Micropickle/vocoder/photos/CAD designs/KiCad/Screenshot from 2026-01-22 20-45-53.png

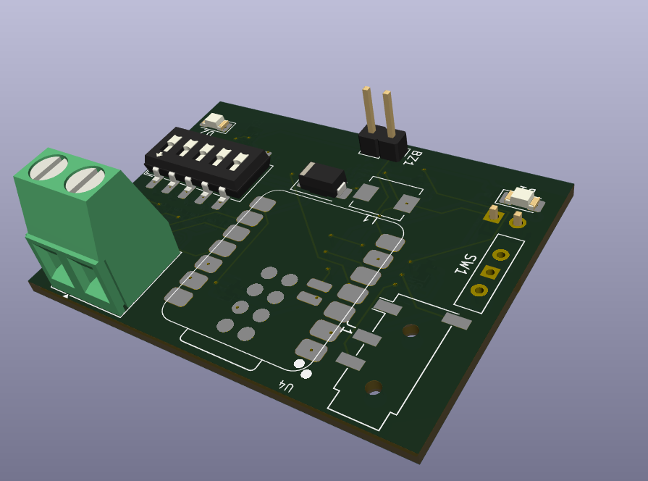
photos/CAD designs/KiCad/Screenshot from 2026-01-22 20-45-53.png
