Micropickle/vocoder/photos/CAD designs/KiCad/Screenshot from 2026-01-23 09-53-42.png

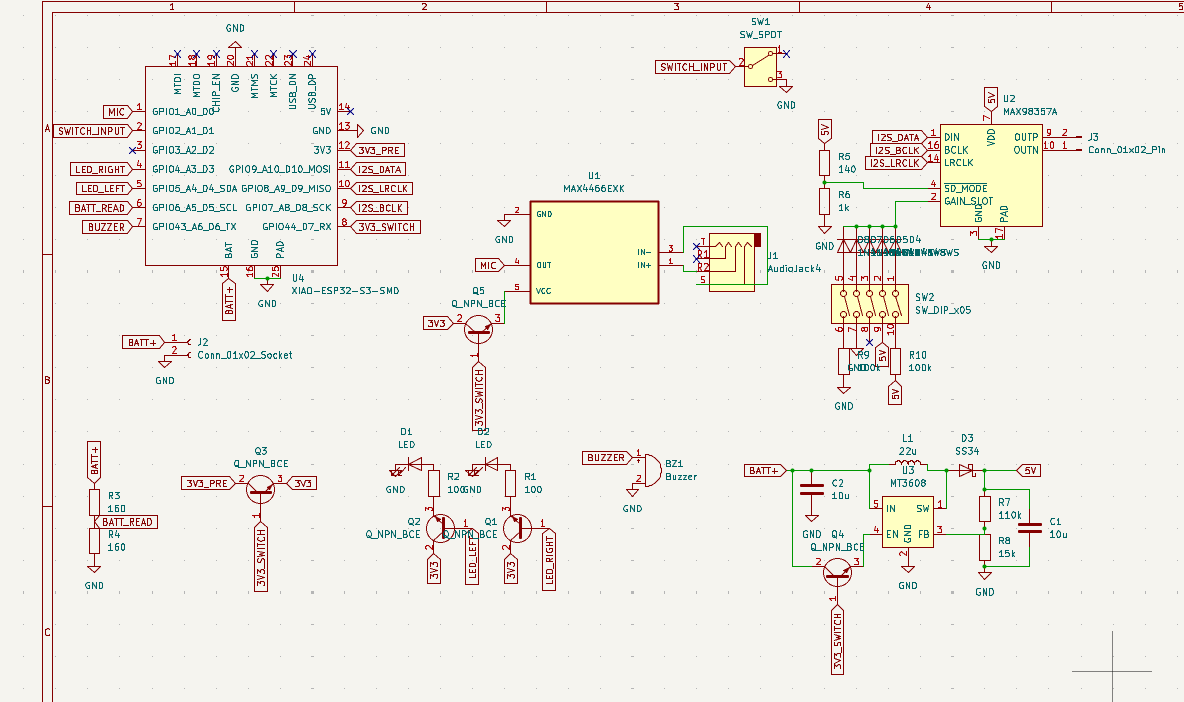
photos/CAD designs/KiCad/Screenshot from 2026-01-23 09-53-42.png
