Micropickle/vocoder/photos/CAD designs/KiCad/Screenshot from 2026-03-05 19-23-13.png

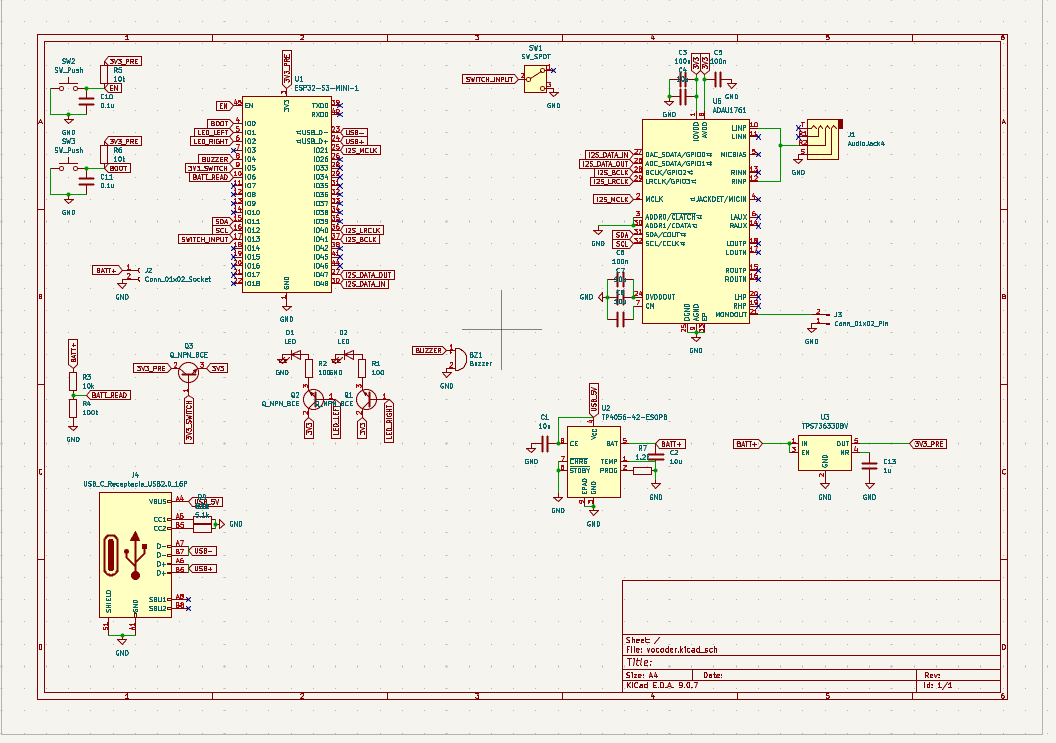
photos/CAD designs/KiCad/Screenshot from 2026-03-05 19-23-13.png
