Micropickle/vocoder/photos/CAD designs/KiCad/Screenshot from 2026-07-01 14-14-26.png

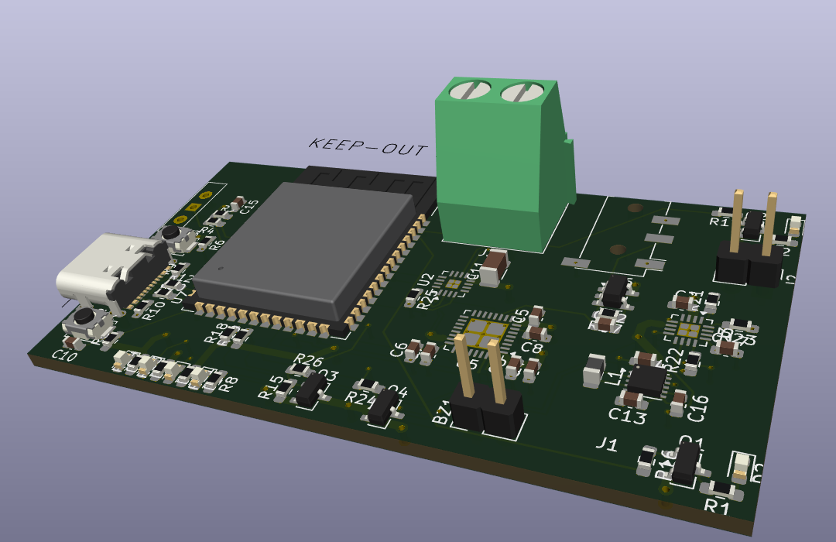
photos/CAD designs/KiCad/Screenshot from 2026-07-01 14-14-26.png
