Micropickle/vocoder/photos/prototype version/IMG_20260123_094632.jpg

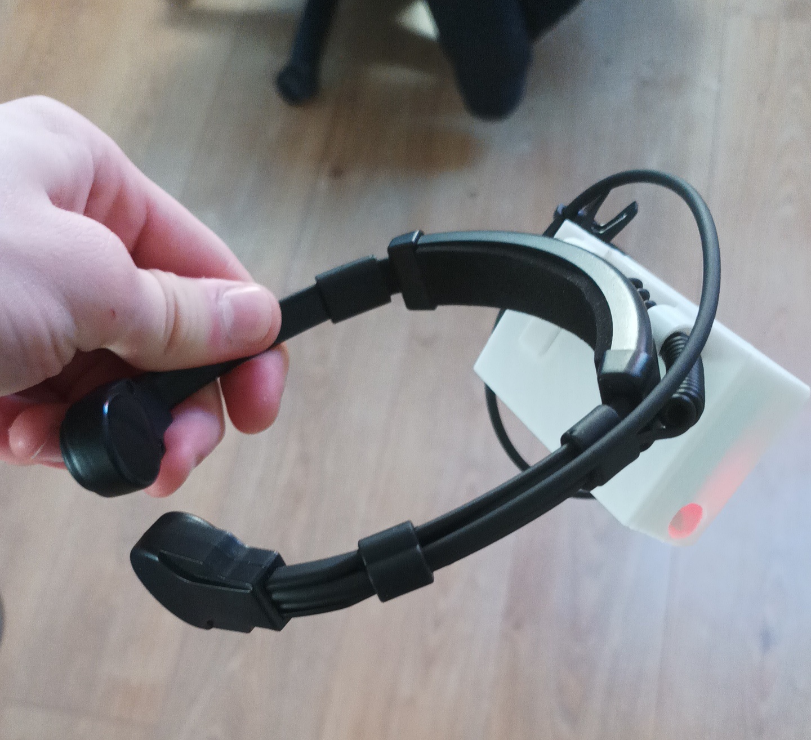
photos/prototype version/IMG_20260123_094632.jpg
