Micropickle/vocoder/photos/prototype version/IMG_20260123_094656.jpg

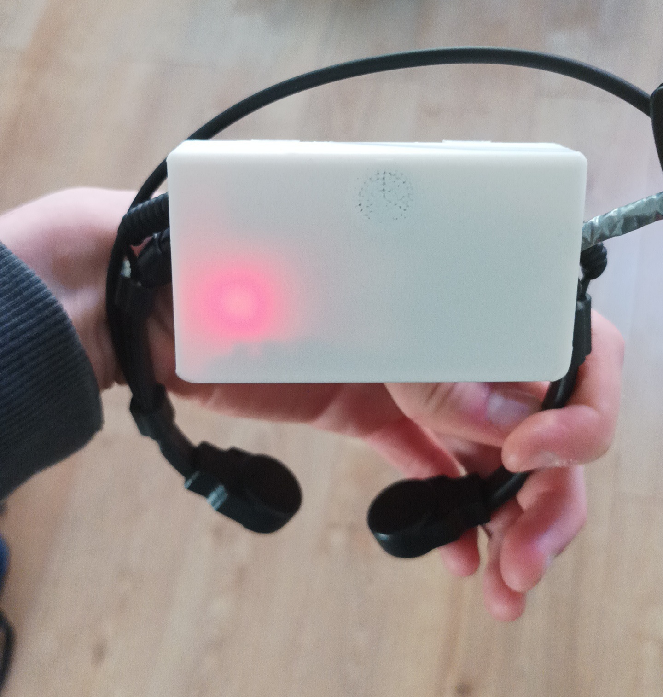
photos/prototype version/IMG_20260123_094656.jpg
