Micropickle/vocoder/photos/prototype version/IMG_20260123_094722.jpg

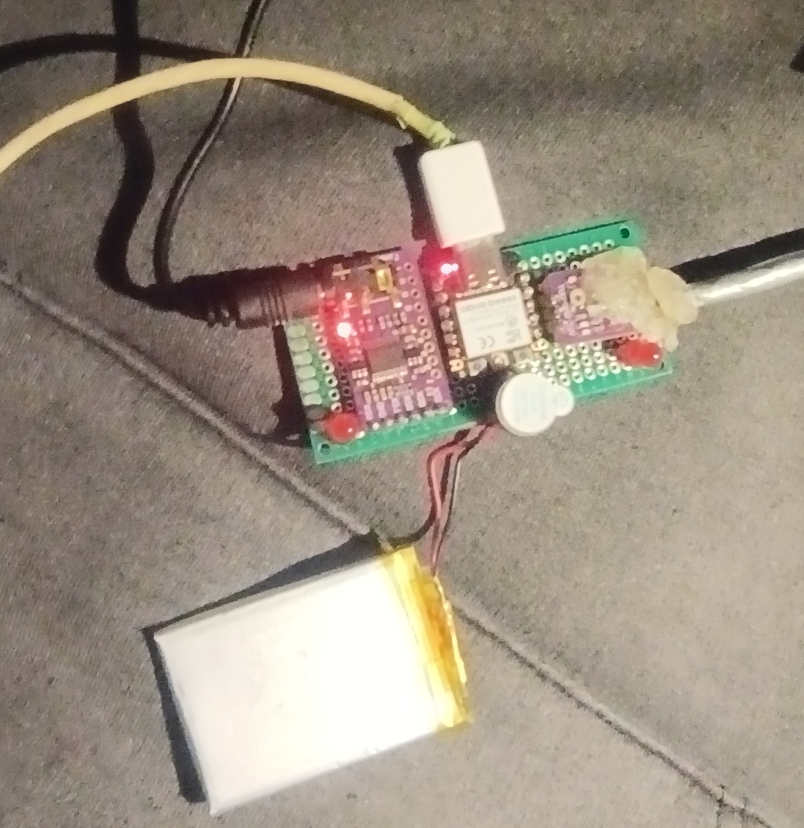
photos/prototype version/IMG_20260123_094722.jpg
